HaraldRieder/Keyboard_Controller/electronics/DSC01424.JPG

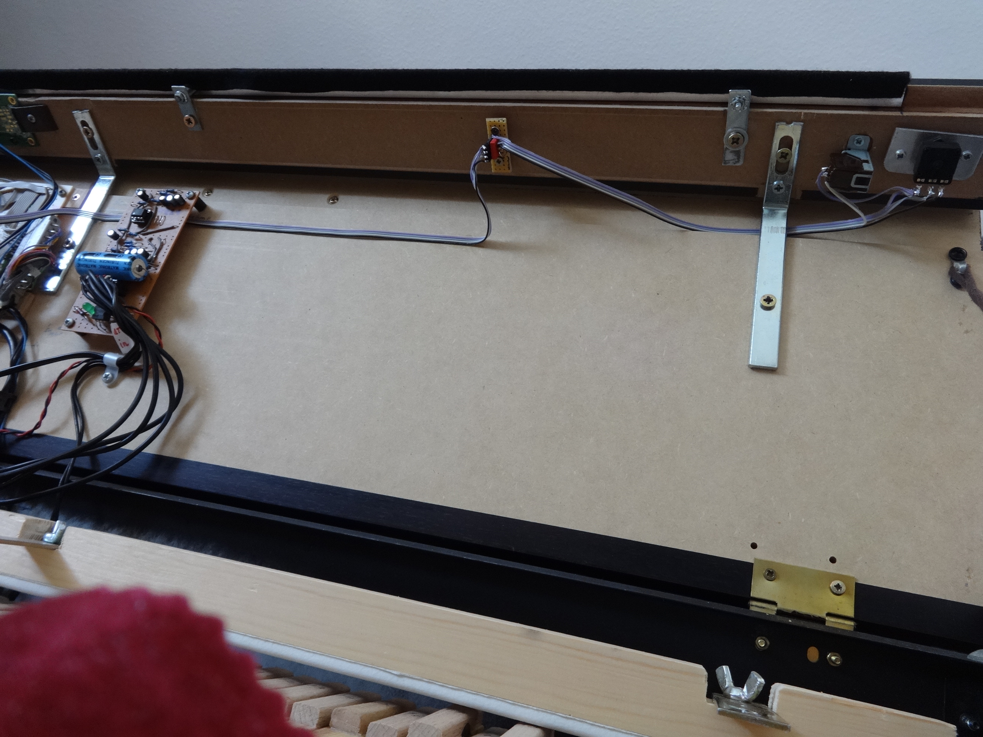
electronics/DSC01424.JPG
